elmo2k3/dabstick_eval/firmware/Src/user_diskio.c

/**
 ******************************************************************************
  * @file    user_diskio.c
  * @author  MCD Tools Team
  * @version V1.0.0
  * @date    07/09/2014 10:33:20
  * @brief   This file includes a diskio driver skeleton to be completed by the user.
  ******************************************************************************
  *
  * COPYRIGHT(c) 2014 STMicroelectronics
  *
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
  ******************************************************************************
  */

/* USER CODE BEGIN 0 */

/* Includes ------------------------------------------------------------------*/
#include <string.h>
#include "ff_gen_drv.h"

#include <stdio.h>
#define BLOCK_SIZE 512

volatile uint8_t ramdisk[1024*100]; // 100kb
/* Disk status */
static volatile DSTATUS Stat = STA_NOINIT;

DSTATUS USER_initialize (void);
DSTATUS USER_status (void);
DRESULT USER_read (BYTE*, DWORD, BYTE);
#if _USE_WRITE == 1
  DRESULT USER_write (const BYTE*, DWORD, BYTE);
#endif /* _USE_WRITE == 1 */
#if _USE_IOCTL == 1
  DRESULT USER_ioctl (BYTE, void*);
#endif /* _USE_IOCTL == 1 */
  
Diskio_drvTypeDef  USER_Driver =
{
  USER_initialize,
  USER_status,
  USER_read, 
#if  _USE_WRITE
  USER_write,
#endif  /* _USE_WRITE == 1 */  
#if  _USE_IOCTL == 1
  USER_ioctl,
#endif /* _USE_IOCTL == 1 */
};


/**
  * @brief  Initializes a Drive
  * @param  None
  * @retval DSTATUS: Operation status
  */
DSTATUS USER_initialize(void)
{
  Stat = STA_NOINIT;
  
  /* USER CODE HERE */
  
  Stat &= ~STA_NOINIT;
  return Stat;
}

/**
  * @brief  Gets Disk Status
  * @param  None
  * @retval DSTATUS: Operation status
  */
DSTATUS USER_status(void)
{
  Stat = STA_NOINIT;
  
  Stat &= ~STA_NOINIT;

  return Stat;
}

/**
  * @brief  Reads Sector(s)
  * @param  *buff: Data buffer to store read data
  * @param  sector: Sector address (LBA)
  * @param  count: Number of sectors to read (1..128)
  * @retval DRESULT: Operation result
  */
DRESULT USER_read(BYTE *buff, DWORD sector, BYTE count)
{
  /* USER CODE HERE */
  uint32_t i;
  uint8_t *address;

  printf("reading %d bytes at %d\r\n",count,sector);

  address = (uint8_t*)((ramdisk + (BLOCK_SIZE * sector)));
  for(i=0;i<(count*BLOCK_SIZE);i++){
      buff[i] = *address++;
  }
  
  return RES_OK;
}

/**
  * @brief  Writes Sector(s)
  * @param  *buff: Data to be written
  * @param  sector: Sector address (LBA)
  * @param  count: Number of sectors to write (1..128)
  * @retval DRESULT: Operation result
  */
#if _USE_WRITE == 1
DRESULT USER_write(const BYTE *buff, DWORD sector, BYTE count)
{ 
  /* USER CODE HERE */
  uint32_t i;
  uint8_t *address;

  printf("writing %d bytes at %d\r\n",count,sector);

  address = (uint8_t*)((ramdisk + (BLOCK_SIZE * sector)));

  for(i=0;i<(count*512);i++){
      *address++ = buff[i];
  }

  return RES_OK;
}
#endif /* _USE_WRITE == 1 */

/**
  * @brief  I/O control operation
  * @param  cmd: Control code
  * @param  *buff: Buffer to send/receive control data
  * @retval DRESULT: Operation result
  */
#if _USE_IOCTL == 1
DRESULT USER_ioctl(BYTE cmd, void *buff)
{
  DRESULT res = RES_ERROR;
  
  /* USER CODE HERE */
  if (Stat & STA_NOINIT) return RES_NOTRDY;
  
  switch (cmd)
  {
  /* Make sure that no pending write process */
  case CTRL_SYNC :
    res = RES_OK;
    break;
  
  /* Get number of sectors on the disk (DWORD) */
  case GET_SECTOR_COUNT :
    *(DWORD*)buff = (1024*100)/ BLOCK_SIZE;
    res = RES_OK;
    break;
  
  /* Get R/W sector size (WORD) */
  case GET_SECTOR_SIZE :
    *(WORD*)buff = BLOCK_SIZE;
    res = RES_OK;
    break;
  
  /* Get erase block size in unit of sector (DWORD) */
  case GET_BLOCK_SIZE :
    *(DWORD*)buff = BLOCK_SIZE;
    break;
  
  default:
    res = RES_PARERR;
  }
  return res;
}
#endif /* _USE_IOCTL == 1 */

/* USER CODE END 0 */

/************************ (C) COPYRIGHT STMicroelectronics *****END OF FILE****/
